strange-v/wifi_clock/src/Cfg.h

#pragma once
#include <Arduino.h>

namespace Cfg
{
	const char wifiApSsid[] = "CL";
	const char wifiApPassword[] = "123456789";
	const unsigned long wifiConnectionTimeout = 30 * 1000;
	const unsigned long wifiAPTimeout = 1 * 60 * 1000;

	const byte pinSda = 4;
	const byte pinScl = 5;
	const byte pinOe = 12;
	const byte pinRtcInt = 14;

	const char version[] = "1.1.1";
}
