strange-v/wifi_clock/src/WebServerConstants.h

#pragma once

const char TEXT_HTML[] = "text/html";
const char APPLICATION_JSON[] = "application/json";
const char JSON_ERROR1[] = "{\"code\":1}";
const char JSON_ERROR2[] = "{\"code\":2}";
const char JSON_ERROR3[] = "{\"code\":3}";
const char JSON_SUCCESS[] = "{\"code\":0}";
